Ka6667/DUCKY/Firmware/duck_clock.ino

#include <Arduino.h>
#include <WiFi.h>
#include <time.h>
#include <Adafruit_GFX.h>
#include <Adafruit_ST7735.h>
#include <DFRobotDFPlayerMini.h>
#include <pgmspace.h>

// ── WiFi ─────────────────────────────────────────────────────
const char* WIFI_SSID     = "isotones";
const char* WIFI_PASSWORD = "Isotones@2020";
const char* NTP_SERVER    = "pool.ntp.org";   
const long  GMT_OFFSET_SEC      = 7200;        // Cairo = UTC+2
const int   DAYLIGHT_OFFSET_SEC = 0;

// ── Pins ─────────────────────────────────────────────────────
#define POT_PIN   2
#define BTN_PIN   3
#define TFT_RST   4
#define TFT_CS    5
#define TFT_DC    7
#define TFT_MOSI  10
#define TFT_MISO  9
#define TFT_SCK   8
#define DF_TX     21
#define DF_RX     20

// ── Screen ───────────────────────────────────────────────────
Adafruit_ST7735 tft = Adafruit_ST7735(TFT_CS, TFT_DC, TFT_MOSI, TFT_SCK, TFT_RST);
#define SCREEN_W 128
#define SCREEN_H 160

// ── DFMini ───────────────────────────────────────────────────
HardwareSerial dfSerial(1);
DFRobotDFPlayerMini dfPlayer;

// ── Modes & Animations ───────────────────────────────────────
enum Mode   { MODE_CLOCK, MODE_TIMER, MODE_STOPWATCH, MODE_MUSIC };
enum AnimID { ANIM_BLINK, ANIM_SLEEP, ANIM_MUSIC, ANIM_SAD };
Mode    currentMode = MODE_CLOCK;
AnimID  currentAnim = ANIM_BLINK;

// ── Button ───────────────────────────────────────────────────
unsigned long btnPressTime        = 0;
int           pressCount          = 0;
bool          btnWasPressed       = false;
unsigned long lastPressCountReset = 0;
#define DOUBLE_PRESS_WINDOW 500
#define HOLD_TIME           2000
#define MUSIC_HOLD_TIME     500

// ── Timer ────────────────────────────────────────────────────
int           timerMinutes    = 1;
bool          timerRunning    = false;
bool          timerSet        = false;
unsigned long timerStartMs    = 0;
unsigned long timerDurationMs = 0;
bool          timerExpired    = false;
unsigned long sadStartMs      = 0;
bool          sadActive       = false;

// ── Stopwatch ────────────────────────────────────────────────
bool          swRunning      = false;
unsigned long swStartMs      = 0;
unsigned long swElapsedMs    = 0;
unsigned long swLapAlertSec  = 10;
unsigned long swLastLap      = 0;

// ── Music ────────────────────────────────────────────────────
bool musicPlaying = false;
int  musicVolume  = 15;

// ── Animation ────────────────────────────────────────────────
int           animFrame     = 0;
unsigned long lastFrameMs   = 0;
unsigned long frameInterval = 200;
unsigned long lastClockRefresh = 0;

#define FRAME_W    120
#define FRAME_H    160
#define FRAME_BYTES (FRAME_W * FRAME_H * 2)  // 38400 bytes per frame

// BLINKING (5 frames)
const uint8_t PROGMEM anim_blink_0[FRAME_BYTES] = {0x00, 0x00, 0x00, 0x00, 0x00, 0x00, 0x00, 0x00, 0x00, 0x00, 0x00, 0x00, 0x00, 0x00, 0x00, 0x00, 
	0x00, 0x00, 0x00, 0x00, 0x00, 0x00, 0x00, 0x00, 0x00, 0x00, 0x00, 0x00, 0x00, 0x00, 0x00, 0x00, 
	0x00, 0x00, 0x00, 0x00, 0x00, 0x00, 0x00, 0x00, 0x00, 0x00, 0x00, 0x00, 0x00, 0x00, 0x00, 0x00, 
	0x00, 0x00, 0x00, 0x00, 0x00, 0x00, 0x00, 0x00, 0x00, 0x00, 0x00, 0x00, 0x00, 0x00, 0x00, 0x00, 
	0x00, 0x00, 0x00, 0x00, 0x00, 0x00, 0x00, 0x00, 0x00, 0x00, 0x00, 0x00, 0x00, 0x00, 0x00, 0x00, 
	0x00, 0x00, 0x00, 0x00, 0x00, 0x00, 0x00, 0x00, 0x00, 0x00, 0x00, 0x00, 0x00, 0x00, 0x00, 0x00, 
	0x00, 0x00, 0x00, 0x00, 0x00, 0x00, 0x00, 0x00, 0x00, 0x00, 0x00, 0x00, 0x00, 0x00, 0x00, 0x00, 
	0x00, 0x00, 0x00, 0x00, 0x00, 0x00, 0x00, 0x00, 0x00, 0x00, 0x00, 0x00, 0x00, 0x00, 0x00, 0x00, 
	0x00, 0x00, 0x00, 0x00, 0x00, 0x00, 0x00, 0x00, 0x00, 0x00, 0x00, 0x00, 0x00, 0x00, 0x00, 0x00, 
	0x00, 0x00, 0x00, 0x00, 0x00, 0x00, 0x00, 0x00, 0x00, 0x00, 0x00, 0x00, 0x00, 0x00, 0x00, 0x00, 
	0x00, 0x00, 0x00, 0x00, 0x00, 0x00, 0x00, 0x00, 0x00, 0x00, 0x00, 0x00, 0x00, 0x00, 0x00, 0x00, 
	0x00, 0x00, 0x00, 0x00, 0x00, 0x00, 0x00, 0x00, 0x00, 0x00, 0x00, 0x00, 0x00, 0x00, 0x00, 0x00, 
	0x00, 0x00, 0x00, 0x00, 0x00, 0x00, 0x00, 0x00, 0x00, 0x00, 0x00, 0x00, 0x00, 0x00, 0x00, 0x00, 
	0x00, 0x00, 0x00, 0x00, 0x00, 0x00, 0x00, 0x00, 0x00, 0x00, 0x00, 0x00, 0x00, 0x00, 0x00, 0x00, 
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
	0xff, 0xff, 0xe0, 0x00, 0x00, 0x00, 0x00, 0x00, 0xff, 0xbe, 0x39, 0xcf, 0x8f, 0x79, 0xff, 0xff, 
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
const uint8_t* const anim_sad[5] PROGMEM = {
  anim_sad_0, anim_sad_1, anim_sad_2, anim_sad_3, anim_sad_4
};

// ─────────────────────────────────────────────────────────────
//  Draw one frame from PROGMEM onto TFT
// ─────────────────────────────────────────────────────────────
void drawFrame(const uint8_t* const* animArray, int frame) {
  const uint8_t* frameData = (const uint8_t*)pgm_read_ptr(&animArray[frame]);
  int xOff = (SCREEN_W - FRAME_W) / 2;  // center 120px on 128px screen
  tft.startWrite();
  tft.setAddrWindow(xOff, 0, FRAME_W, FRAME_H);
  for (int i = 0; i < FRAME_BYTES; i += 2) {
    uint8_t hi = pgm_read_byte(frameData + i);
    uint8_t lo = pgm_read_byte(frameData + i + 1);
    tft.pushColor((hi << 8) | lo);
  }
  tft.endWrite();
}

// ─────────────────────────────────────────────────────────────
//  Time helpers
// ─────────────────────────────────────────────────────────────
struct tm getLocalTime() {
  struct tm ti = {};
  time_t now;
  time(&now);
  localtime_r(&now, &ti);
  return ti;
}

bool isNightTime() {
  struct tm ti = getLocalTime();
  return (ti.tm_hour >= 22 || ti.tm_hour < 6);
}

// ─────────────────────────────────────────────────────────────
//  Clock face overlay
// ─────────────────────────────────────────────────────────────
void drawClockFace() {
  struct tm ti = getLocalTime();
  char timeBuf[9], dateBuf[12];
  snprintf(timeBuf, sizeof(timeBuf), "%02d:%02d:%02d",
           ti.tm_hour, ti.tm_min, ti.tm_sec);
  snprintf(dateBuf, sizeof(dateBuf), "%04d-%02d-%02d",
           ti.tm_year + 1900, ti.tm_mon + 1, ti.tm_mday);

  tft.fillRect(0, SCREEN_H - 36, SCREEN_W, 36, ST77XX_BLACK);
  tft.setTextColor(ST77XX_WHITE);
  tft.setTextSize(2);
  tft.setCursor(4, SCREEN_H - 32);
  tft.print(timeBuf);
  tft.setTextSize(1);
  tft.setCursor(10, SCREEN_H - 12);
  tft.print(dateBuf);
}

// ─────────────────────────────────────────────────────────────
//  Timer screen
// ─────────────────────────────────────────────────────────────
void drawTimerScreen() {
  tft.fillScreen(ST77XX_BLACK);
  tft.setTextColor(ST77XX_CYAN);
  tft.setTextSize(2);
  tft.setCursor(10, 20);
  tft.print("TIMER");

  if (!timerRunning) {
    tft.setTextSize(1);
    tft.setTextColor(ST77XX_YELLOW);
    tft.setCursor(10, 55);
    tft.print("Pot = set minutes");
    tft.setTextSize(3);
    tft.setTextColor(ST77XX_WHITE);
    tft.setCursor(30, 80);
    char buf[6];
    snprintf(buf, sizeof(buf), "%02d:00", timerMinutes);
    tft.print(buf);
    tft.setTextSize(1);
    tft.setTextColor(ST77XX_GREEN);
    tft.setCursor(10, 130);
    tft.print("Press to START");
  } else {
    unsigned long elapsed   = millis() - timerStartMs;
    unsigned long remaining = (elapsed < timerDurationMs) ? (timerDurationMs - elapsed) : 0;
    int remSec = remaining / 1000;
    int remMin = remSec / 60;
    remSec %= 60;
    tft.setTextSize(3);
    tft.setTextColor(ST77XX_WHITE);
    tft.setCursor(20, 80);
    char buf[6];
    snprintf(buf, sizeof(buf), "%02d:%02d", remMin, remSec);
    tft.print(buf);

    if (remaining == 0 && !timerExpired) {
      timerExpired = true;
      timerRunning = false;
      sadStartMs   = millis();
      sadActive    = true;
      dfPlayer.play(1);
    }
  }
}

// ─────────────────────────────────────────────────────────────
//  Stopwatch screen
// ─────────────────────────────────────────────────────────────
void drawStopwatchScreen() {
  unsigned long elapsed = swRunning ? (millis() - swStartMs + swElapsedMs) : swElapsedMs;
  unsigned long cs  = (elapsed / 10) % 100;
  unsigned long sec = (elapsed / 1000) % 60;
  unsigned long mn  = (elapsed / 60000) % 60;

  tft.fillScreen(ST77XX_BLACK);
  tft.setTextColor(ST77XX_MAGENTA);
  tft.setTextSize(2);
  tft.setCursor(4, 20);
  tft.print("STOPWATCH");

  tft.setTextSize(3);
  tft.setTextColor(ST77XX_WHITE);
  tft.setCursor(4, 70);
  char buf[9];
  snprintf(buf, sizeof(buf), "%02lu:%02lu.%02lu", mn, sec, cs);
  tft.print(buf);

  tft.setTextSize(1);
  tft.setTextColor(ST77XX_YELLOW);
  tft.setCursor(4, 120);
  tft.print("Lap alert: ");
  tft.print(swLapAlertSec);
  tft.print("s");

  tft.setTextColor(ST77XX_GREEN);
  tft.setCursor(4, 140);
  if (!swRunning) tft.print("Press = START");
  else            tft.print("Press=STOP  Hold=RESET");

  if (swRunning && swLapAlertSec > 0) {
    unsigned long elapsedSec = elapsed / 1000;
    if (elapsedSec > 0 && elapsedSec % swLapAlertSec == 0 && elapsedSec != swLastLap) {
      swLastLap = elapsedSec;
      dfPlayer.play(2);
    }
  }
}

// ─────────────────────────────────────────────────────────────
//  Music screen overlay
// ─────────────────────────────────────────────────────────────
void drawMusicScreen() {
  tft.fillRect(0, SCREEN_H - 36, SCREEN_W, 36, ST77XX_BLACK);
  tft.setTextColor(ST77XX_GREEN);
  tft.setTextSize(1);
  tft.setCursor(4, SCREEN_H - 32);
  tft.print(musicPlaying ? "PLAYING" : "STOPPED");
  tft.setCursor(4, SCREEN_H - 18);
  tft.print("VOL: ");
  tft.print(musicVolume);
  tft.print(" / 30");
  tft.setCursor(4, SCREEN_H - 8);
  tft.print("Press=play/stop  Hold=back");
}

// ─────────────────────────────────────────────────────────────
//  Animation tick
// ─────────────────────────────────────────────────────────────
void updateAnimation() {
  unsigned long now = millis();
  const uint8_t* const* animSet = nullptr;

  if (sadActive) {
    animSet = anim_sad;
    frameInterval = 150;
    if (now - sadStartMs > 30000) sadActive = false;
  } else if (currentMode == MODE_MUSIC) {
    animSet = anim_music;
    frameInterval = 120;
  } else if (currentMode == MODE_CLOCK) {
    animSet = isNightTime() ? anim_sleep : anim_blink;
    frameInterval = isNightTime() ? 600 : 300;
  }

  if (animSet && now - lastFrameMs > frameInterval) {
    lastFrameMs = now;
    drawFrame(animSet, animFrame);
    animFrame = (animFrame + 1) % 5;
    if (currentMode == MODE_CLOCK) drawClockFace();
    if (currentMode == MODE_MUSIC) drawMusicScreen();
  }
}

// ─────────────────────────────────────────────────────────────
//  Potentiometer
// ─────────────────────────────────────────────────────────────
void handlePotentiometer() {
  int raw = analogRead(POT_PIN);  // 0–4095 on ESP32

  if (currentMode == MODE_TIMER && !timerRunning) {
    timerMinutes = map(raw, 0, 4095, 1, 60);
  } else if (currentMode == MODE_STOPWATCH) {
    swLapAlertSec = map(raw, 0, 4095, 5, 120);
  } else if (currentMode == MODE_MUSIC) {
    int newVol = map(raw, 0, 4095, 0, 30);
    if (newVol != musicVolume) {
      musicVolume = newVol;
      dfPlayer.volume(musicVolume);
    }
  }
  // Clock mode: wire TFT BL to a PWM pin to enable brightness control
}

// ─────────────────────────────────────────────────────────────
//  Button handler
// ─────────────────────────────────────────────────────────────
void handleButton() {
  bool pressed = (digitalRead(BTN_PIN) == LOW);
  unsigned long now = millis();

  if (pressed && !btnWasPressed) {
    btnPressTime  = now;
    btnWasPressed = true;
  }

  if (!pressed && btnWasPressed) {
    unsigned long holdDuration = now - btnPressTime;
    btnWasPressed = false;

    // 2s hold → return to clock
    if (holdDuration >= HOLD_TIME) {
      if (currentMode == MODE_STOPWATCH) {
        swRunning = false; swElapsedMs = 0; swLastLap = 0;
      }
      if (currentMode == MODE_MUSIC && musicPlaying) {
        dfPlayer.stop(); musicPlaying = false;
      }
      currentMode = MODE_CLOCK;
      tft.fillScreen(ST77XX_BLACK);
      pressCount = 0;
      return;
    }

    // 0.5s hold in clock → enter music
    if (holdDuration >= MUSIC_HOLD_TIME && currentMode == MODE_CLOCK) {
      currentMode = MODE_MUSIC;
      tft.fillScreen(ST77XX_BLACK);
      pressCount = 0;
      return;
    }

    // Short press
    pressCount++;
    lastPressCountReset = now;
  }

  // Evaluate press count after double-press window closes
  if (pressCount > 0 && (millis() - lastPressCountReset > DOUBLE_PRESS_WINDOW)) {
    if (currentMode == MODE_CLOCK) {
      if (pressCount == 1) {
        currentMode = MODE_TIMER;
        timerRunning = false; timerSet = false; timerExpired = false;
        tft.fillScreen(ST77XX_BLACK);
      } else {
        currentMode = MODE_STOPWATCH;
        swRunning = false; swElapsedMs = 0; swLastLap = 0;
        tft.fillScreen(ST77XX_BLACK);
      }
    } else if (currentMode == MODE_TIMER) {
      if (!timerRunning && !timerSet) {
        timerDurationMs = (unsigned long)timerMinutes * 60000UL;
        timerStartMs    = millis();
        timerRunning    = true;
        timerSet        = true;
        timerExpired    = false;
      } else if (timerRunning) {
        timerRunning = false;
      }
    } else if (currentMode == MODE_STOPWATCH) {
      if (!swRunning) {
        swStartMs = millis(); swRunning = true;
      } else {
        swElapsedMs += millis() - swStartMs; swRunning = false;
      }
    } else if (currentMode == MODE_MUSIC) {
      if (musicPlaying) {
        dfPlayer.stop(); musicPlaying = false;
      } else {
        dfPlayer.play(3); musicPlaying = true;
      }
    }
    pressCount = 0;
  }

  // Visual hold feedback (red bar at top)
  if (btnWasPressed && (millis() - btnPressTime >= HOLD_TIME) && currentMode != MODE_CLOCK) {
    tft.fillRect(0, 0, SCREEN_W, 10, ST77XX_RED);
  }
}

// ─────────────────────────────────────────────────────────────
//  Setup
// ─────────────────────────────────────────────────────────────
void setup() {
  Serial.begin(115200);

  // TFT
  tft.initR(INITR_BLACKTAB);
  tft.setRotation(0);
  tft.fillScreen(ST77XX_BLACK);

  // Button
  pinMode(BTN_PIN, INPUT_PULLUP);

  // DFMini
  dfSerial.begin(9600, SERIAL_8N1, DF_RX, DF_TX);
  if (dfPlayer.begin(dfSerial)) {
    dfPlayer.volume(15);
    Serial.println("DFMini ready");
  } else {
    Serial.println("DFMini not found");
  }

  // WiFi + NTP
  tft.setTextColor(ST77XX_CYAN);
  tft.setTextSize(1);
  tft.setCursor(4, 60);
  tft.print("Connecting WiFi...");

  WiFi.begin(WIFI_SSID, WIFI_PASSWORD);
  int tries = 0;
  while (WiFi.status() != WL_CONNECTED && tries < 20) {
    delay(500);
    tries++;
  }

  if (WiFi.status() == WL_CONNECTED) {
    configTime(GMT_OFFSET_SEC, DAYLIGHT_OFFSET_SEC, NTP_SERVER);
    tft.fillScreen(ST77XX_BLACK);
    tft.setCursor(4, 60);
    tft.setTextColor(ST77XX_GREEN);
    tft.print("Time synced!");
    delay(1000);
  } else {
    tft.fillScreen(ST77XX_BLACK);
    tft.setCursor(4, 60);
    tft.setTextColor(ST77XX_RED);
    tft.print("No WiFi - manual time set");
    struct timeval tv = { .tv_sec = 1735728000 };
    settimeofday(&tv, nullptr);
    delay(2000);
  }

  tft.fillScreen(ST77XX_BLACK);
}

// ─────────────────────────────────────────────────────────────
//  Loop
// ─────────────────────────────────────────────────────────────
void loop() {
  handleButton();
  handlePotentiometer();

  switch (currentMode) {
    case MODE_CLOCK:
      updateAnimation();
      break;
    case MODE_TIMER:
      if (millis() - lastClockRefresh > 250) {
        lastClockRefresh = millis();
        drawTimerScreen();
      }
      if (sadActive) updateAnimation();
      break;
    case MODE_STOPWATCH:
      if (millis() - lastClockRefresh > 50) {
        lastClockRefresh = millis();
        drawStopwatchScreen();
      }
      break;
    case MODE_MUSIC:
      updateAnimation();
      break;
  }
}
